aronaut/LoRa-APRS-Gateway-HAT-for-Raspberry-Pi/Pictures/LoRa_APRS_1.jpg

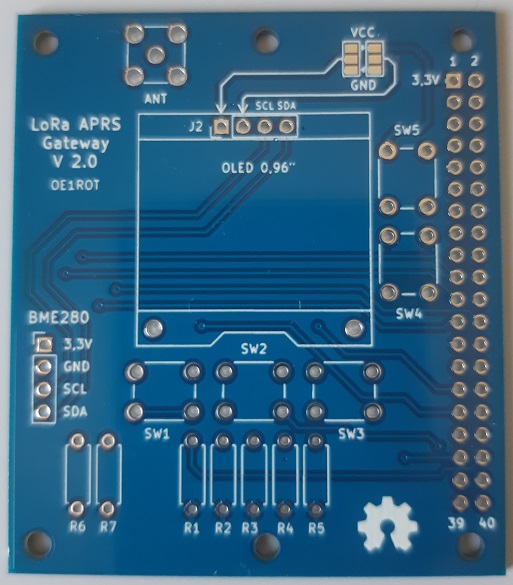
Pictures/LoRa_APRS_1.jpg
